liebman/ESPNTPServer/src/DialogInput_plain_10.h

/*
 * DialogInput_plain_10.h
 *
 *  Created on: Mar 4, 2018
 *      Author: chris.l
 */

#ifndef DIALOGINPUT_PLAIN_10_H_
#define DIALOGINPUT_PLAIN_10_H_

// Created by http://oleddisplay.squix.ch/ Consider a donation
// In case of problems make sure that you are using the font file with the correct version!
const uint8_t DialogInput_plain_10[] PROGMEM = {
    0x06, // Width: 6
    0x0D, // Height: 13
    0x20, // First Char: 32
    0xE0, // Numbers of Chars: 224

    // Jump Table:
    0xFF, 0xFF, 0x00, 0x06,  // 32:65535
    0x00, 0x00, 0x08, 0x06,  // 33:0
    0x00, 0x08, 0x09, 0x06,  // 34:8
    0x00, 0x11, 0x0B, 0x06,  // 35:17
    0x00, 0x1C, 0x0C, 0x06,  // 36:28
    0x00, 0x28, 0x0C, 0x06,  // 37:40
    0x00, 0x34, 0x0C, 0x06,  // 38:52
    0x00, 0x40, 0x07, 0x06,  // 39:64
    0x00, 0x47, 0x08, 0x06,  // 40:71
    0x00, 0x4F, 0x08, 0x06,  // 41:79
    0x00, 0x57, 0x0B, 0x06,  // 42:87
    0x00, 0x62, 0x0B, 0x06,  // 43:98
    0x00, 0x6D, 0x06, 0x06,  // 44:109
    0x00, 0x73, 0x09, 0x06,  // 45:115
    0x00, 0x7C, 0x06, 0x06,  // 46:124
    0x00, 0x82, 0x0B, 0x06,  // 47:130
    0x00, 0x8D, 0x0C, 0x06,  // 48:141
    0x00, 0x99, 0x0C, 0x06,  // 49:153
    0x00, 0xA5, 0x0C, 0x06,  // 50:165
    0x00, 0xB1, 0x0C, 0x06,  // 51:177
    0x00, 0xBD, 0x0B, 0x06,  // 52:189
    0x00, 0xC8, 0x0C, 0x06,  // 53:200
    0x00, 0xD4, 0x0C, 0x06,  // 54:212
    0x00, 0xE0, 0x0B, 0x06,  // 55:224
    0x00, 0xEB, 0x0C, 0x06,  // 56:235
    0x00, 0xF7, 0x0C, 0x06,  // 57:247
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
    0x00,0x00,0xF8,0x03,0x48,0x00,0x48,0x00,0x48,0x00,0x48, // 70
    0x00,0x00,0xF0,0x01,0x18,0x03,0x08,0x02,0x48,0x02,0xD0,0x03,    // 71
    0x00,0x00,0xF8,0x03,0x40,0x00,0x40,0x00,0x40,0x00,0xF8,0x03,    // 72
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
};




#endif /* DIALOGINPUT_PLAIN_10_H_ */
