liebman/ESPNTPServer/src/ESPNTPServerVersion.h

/*
 * ESPNTPServerVersion.h
 *
 *  Created on: Jun 17, 2018
 *      Author: chris.l
 */

#ifndef ESPNTPSERVERVERSION_H_
#define ESPNTPSERVERVERSION_H_

const char* ESPNTP_SERVER_VERSION = "1.0.2";


#endif /* ESPNTPSERVERVERSION_H_ */
